circuitsable/SCARTCouplers/kicad projects/scart-mtf-ftm/scart-mtf-ftm.kicad_sch

## KiCad design kicad projects/scart-mtf-ftm/scart-mtf-ftm.kicad_sch (2025-03-22)

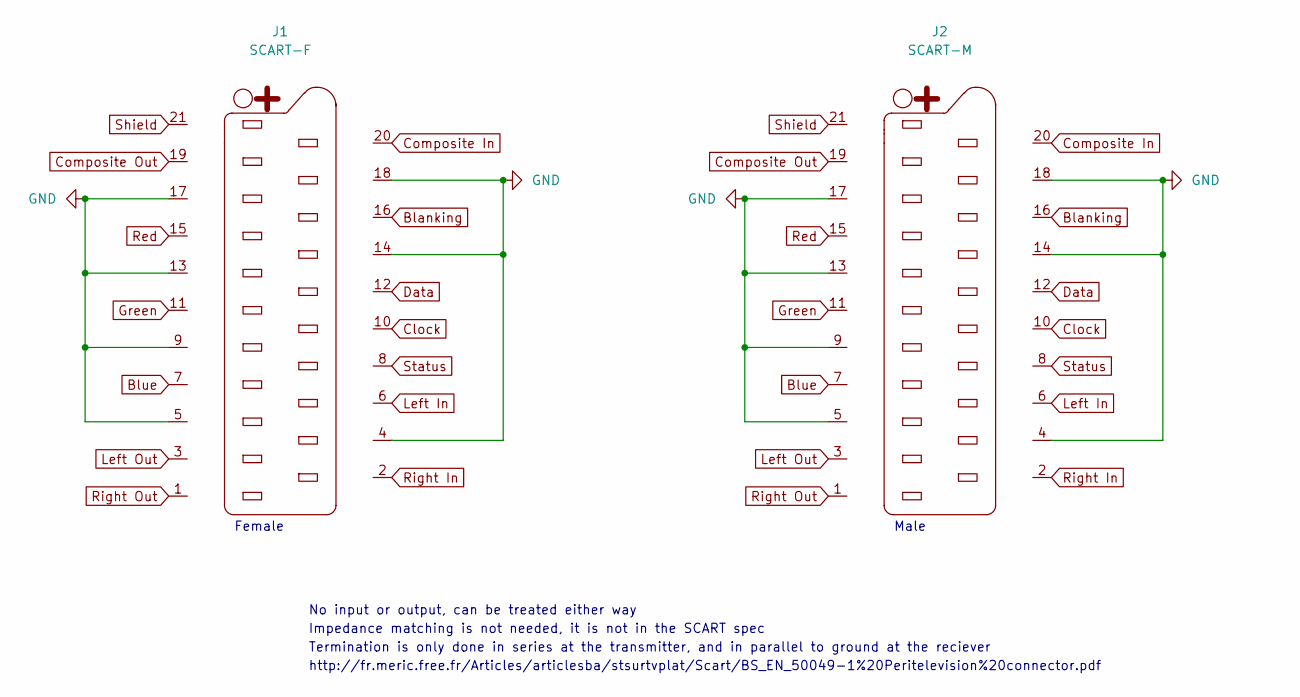
[picture p12: schematic scart-mtf-ftm.kicad_sch]

Parts:
J1: SCART-F; KYCON_SCART_K-SCARTX-022_Horizontal
J2: SCART-M; Male_SCART

Connections:
Blanking: J1.16, J2.16
Blue: J1.7, J2.7
Clock: J1.10, J2.10
Composite In: J1.20, J2.20
Composite Out: J1.19, J2.19
Data: J1.12, J2.12
GND: J1.4, J1.5, J1.9, J1.13, J1.14, J1.17, J1.18, J2.4, J2.5, J2.9, J2.13, J2.14, J2.17, J2.18
Green: J1.11, J2.11
Left In: J1.6, J2.6
Left Out: J1.3, J2.3
Red: J1.15, J2.15
Right In: J1.2, J2.2
Right Out: J1.1, J2.1
Shield: J1.21, J2.21
Status: J1.8, J2.8

Notes on the sheet:
Termination is only done in series at the transmitter, and in parallel to ground at the reciever
Impedance matching is not needed, it is not in the SCART spec
No input or output, can be treated either way
Female
Male
http://fr.meric.free.fr/Articles/articlesba/stsurtvplat/Scart/BS_EN_50049-1%20Peritelevision%20connector.pdf
